deathkiller-mex/Angle-Caliper/Code/pics/Screenshot 2026-09-11 131137.png

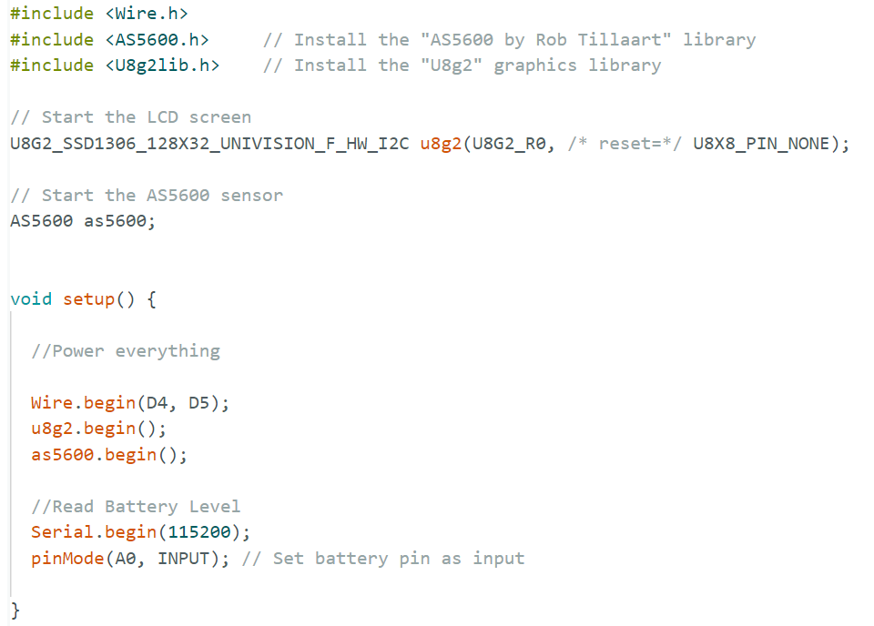
Code/pics/Screenshot 2026-09-11 131137.png
