deathkiller-mex/Angle-Caliper/Schematics/shematic.png

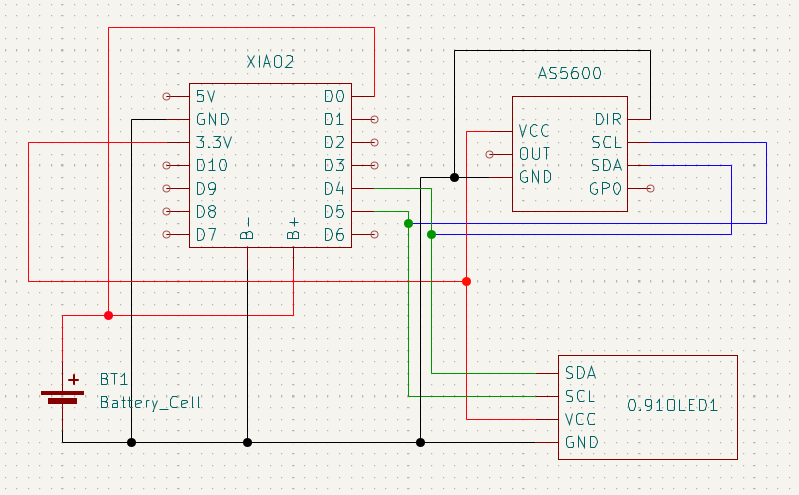
Schematics/shematic.png
