deathkiller-mex/Angle-Caliper/CAD/Pic parts/AS5600.png

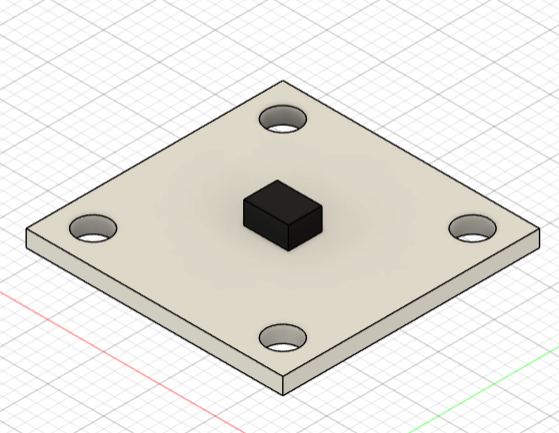
CAD/Pic parts/AS5600.png
