deathkiller-mex/Angle-Caliper/CAD/Pic parts/bottom cover down.png

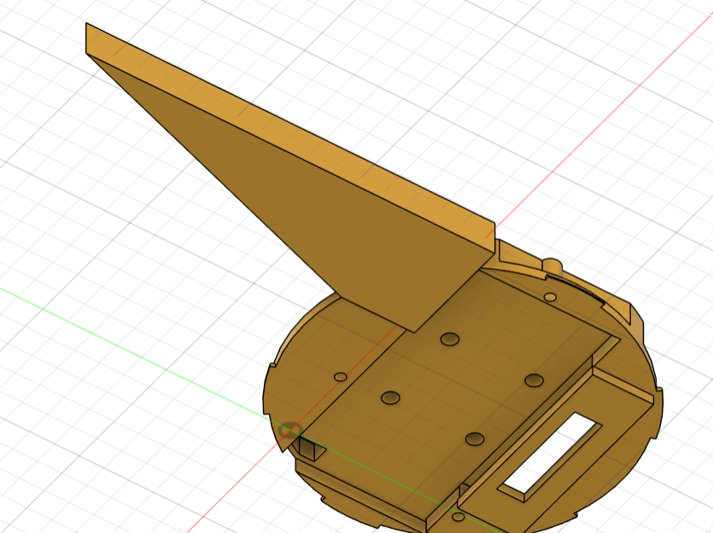
CAD/Pic parts/bottom cover down.png
