deathkiller-mex/Angle-Caliper/CAD/Pic parts/bottom cover.png

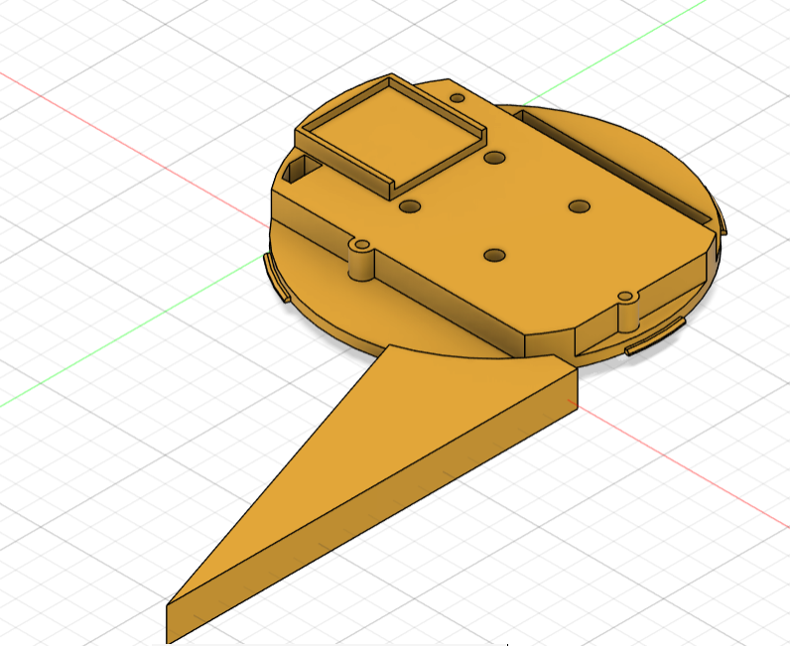
CAD/Pic parts/bottom cover.png
