deathkiller-mex/Angle-Caliper/CAD/Pic parts/LCD screen.png

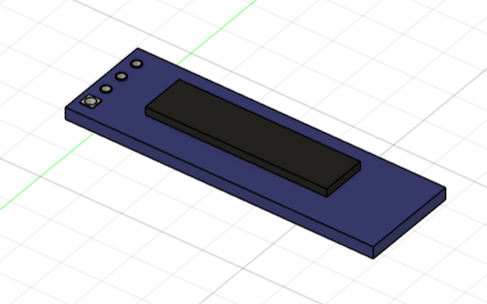
CAD/Pic parts/LCD screen.png
