deathkiller-mex/Angle-Caliper/CAD/Pic parts/lid.png

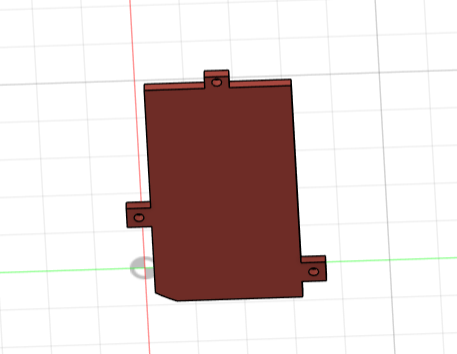
CAD/Pic parts/lid.png
