deathkiller-mex/Angle-Caliper/CAD/Pic parts/magnet cover.png

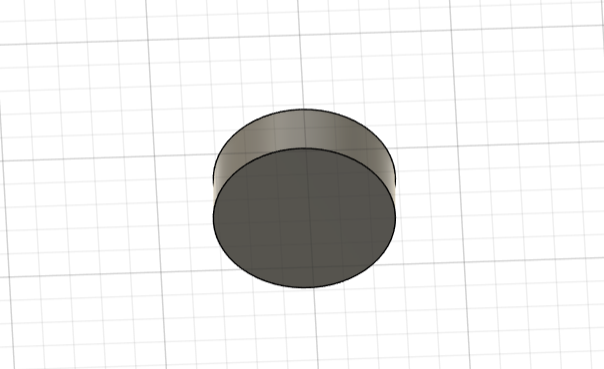
CAD/Pic parts/magnet cover.png
