deathkiller-mex/Angle-Caliper/CAD/Pic parts/v1/bottom cover up.png

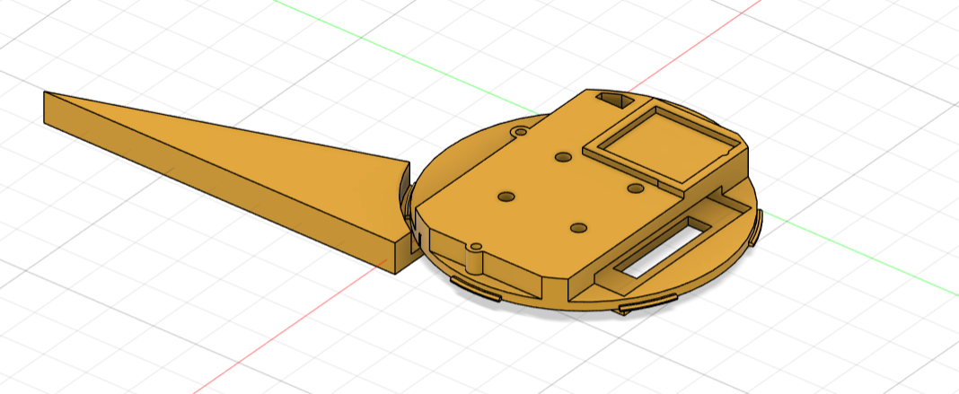
CAD/Pic parts/v1/bottom cover up.png
