deathkiller-mex/Angle-Caliper/CAD/Pic parts/v1/caliper bottom.png

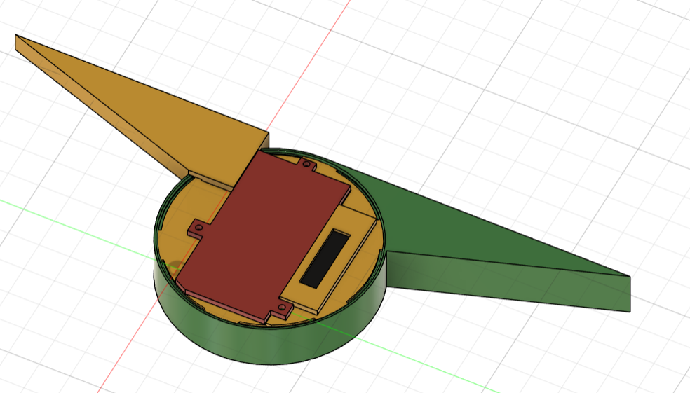
CAD/Pic parts/v1/caliper bottom.png
