deathkiller-mex/Angle-Caliper/CAD/Pic parts/v1/top cover.png

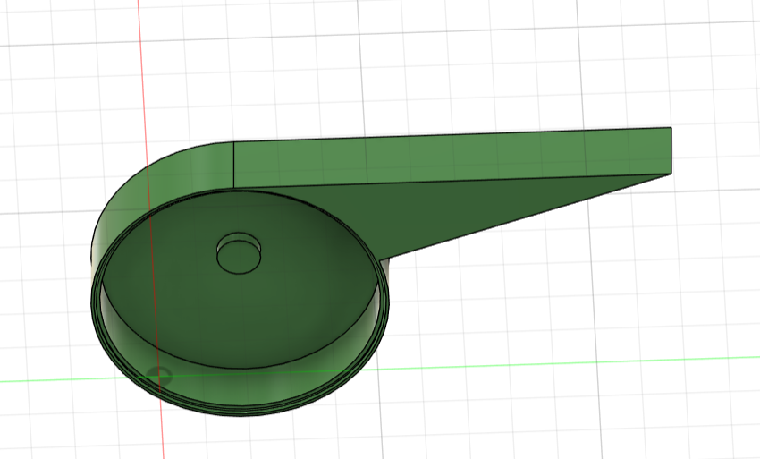
CAD/Pic parts/v1/top cover.png
