deathkiller-mex/Angle-Caliper/CAD/Pic parts/whole assmbly 2.png

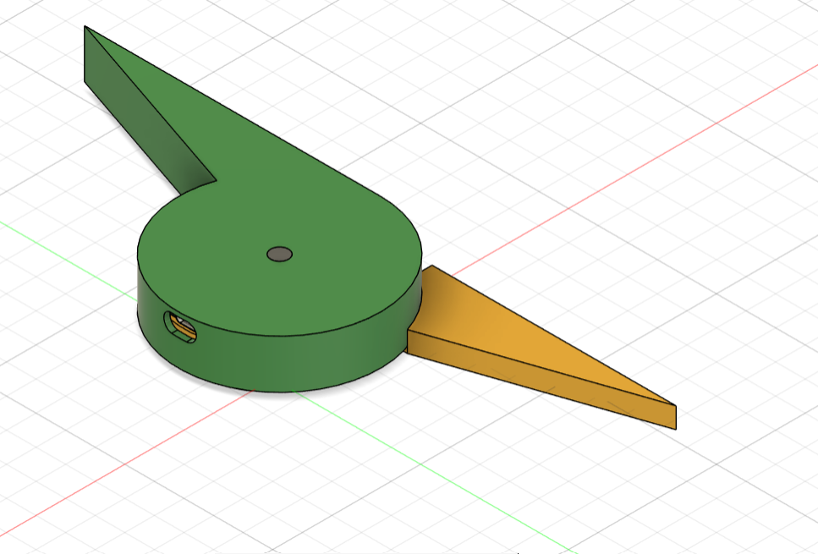
CAD/Pic parts/whole assmbly 2.png
