deathkiller-mex/Angle-Caliper/CAD/Pic parts/bottom cover assembled down.png

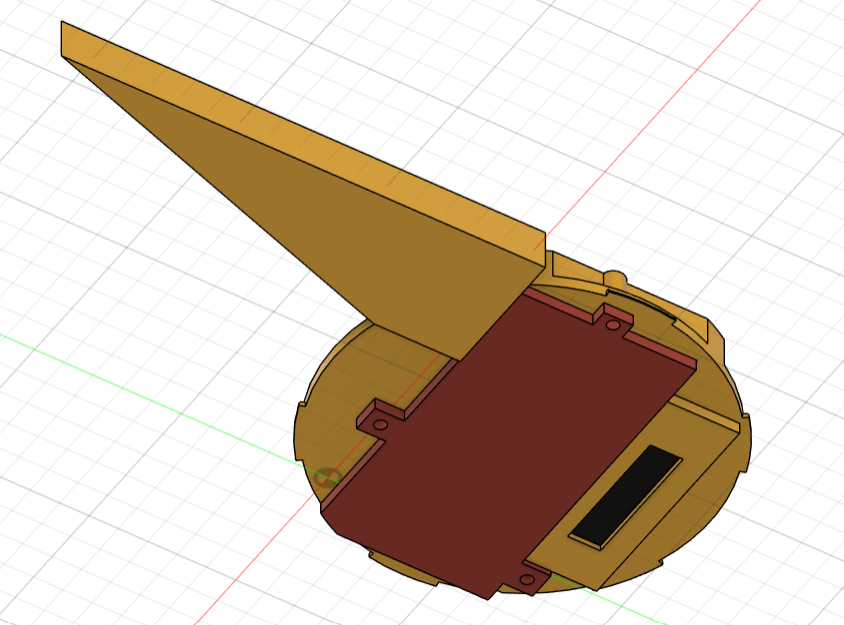
CAD/Pic parts/bottom cover assembled down.png
