deathkiller-mex/Angle-Caliper/CAD/Pic parts/bottom cover assembled up.png

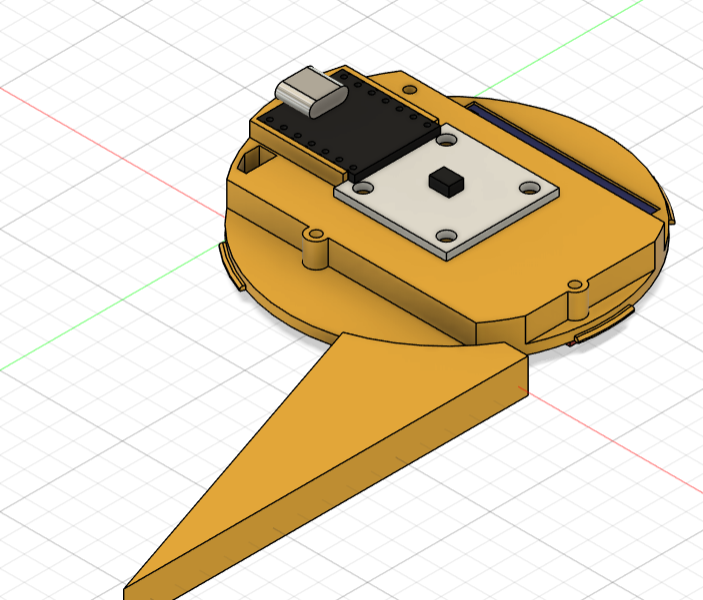
CAD/Pic parts/bottom cover assembled up.png
