deathkiller-mex/Angle-Caliper/CAD/Pic parts/whole assembly.png

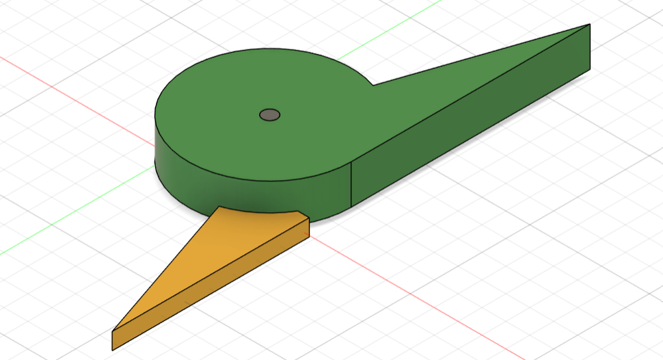
CAD/Pic parts/whole assembly.png
